Miceuz/triac-bloc/triac bloc top.jpg

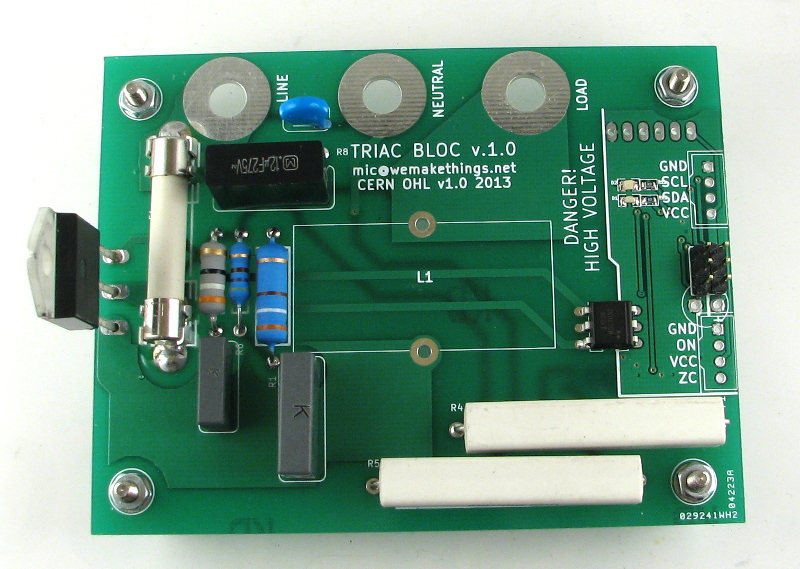
triac bloc top.jpg
