Miceuz/triac-bloc/zc-scope.png

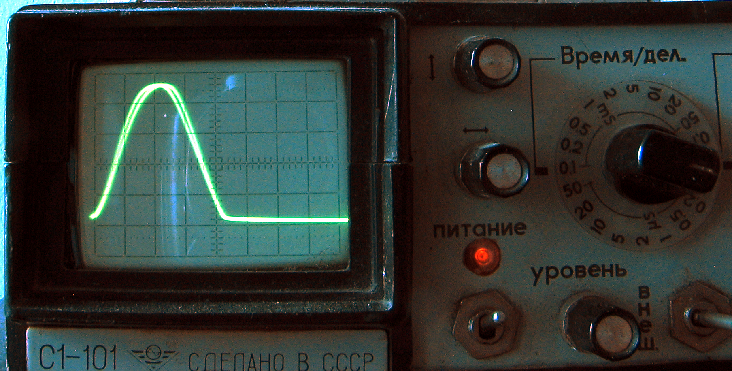
zc-scope.png
