Miceuz/triac-bloc/power-vs-cond-angle.png

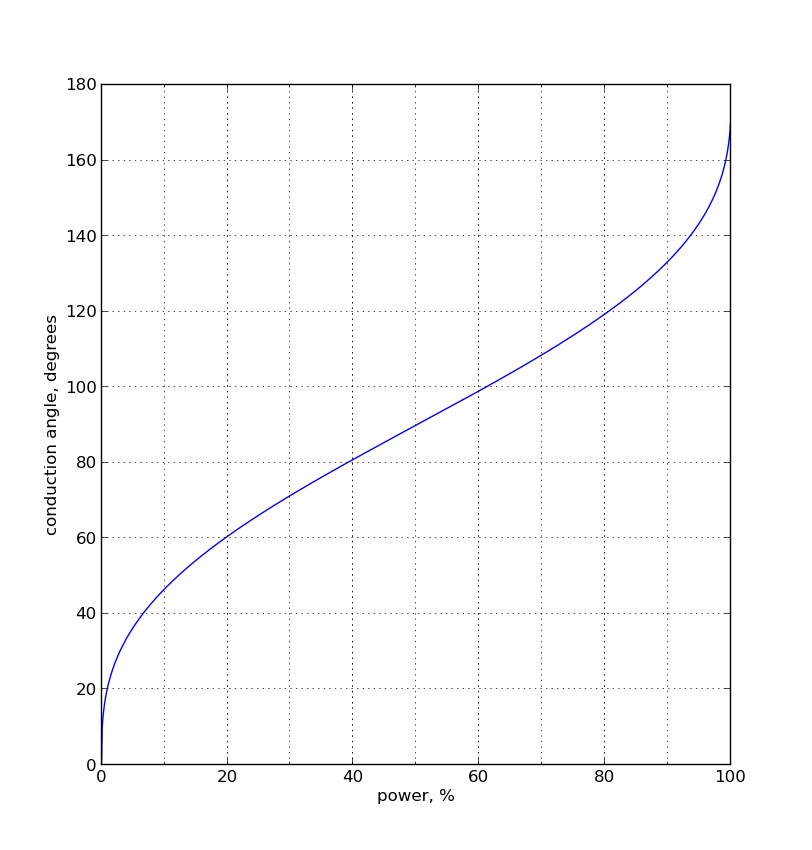
power-vs-cond-angle.png
