Miceuz/triac-bloc/ssr.png

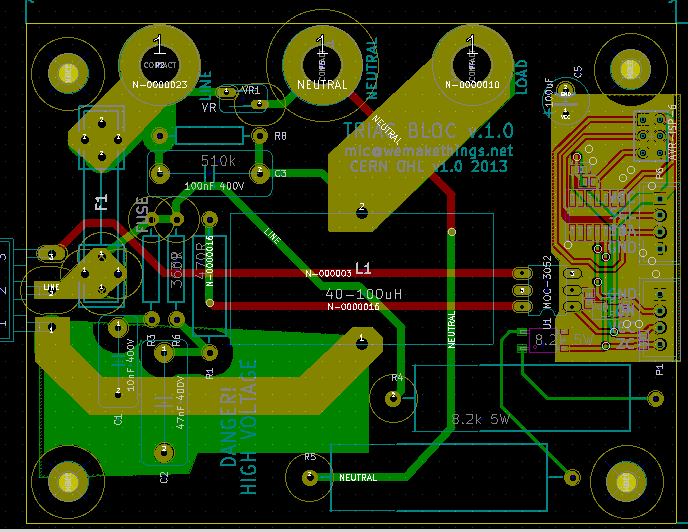
ssr.png
