Miceuz/triac-bloc/triac bloc bottom.jpg

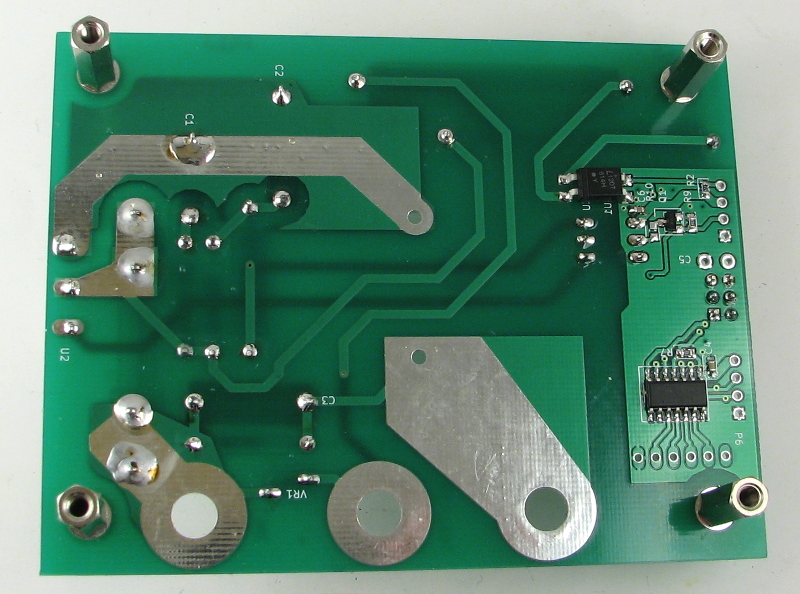
triac bloc bottom.jpg
