Miceuz/triac-bloc/experiment1/impulse-response-linear.png

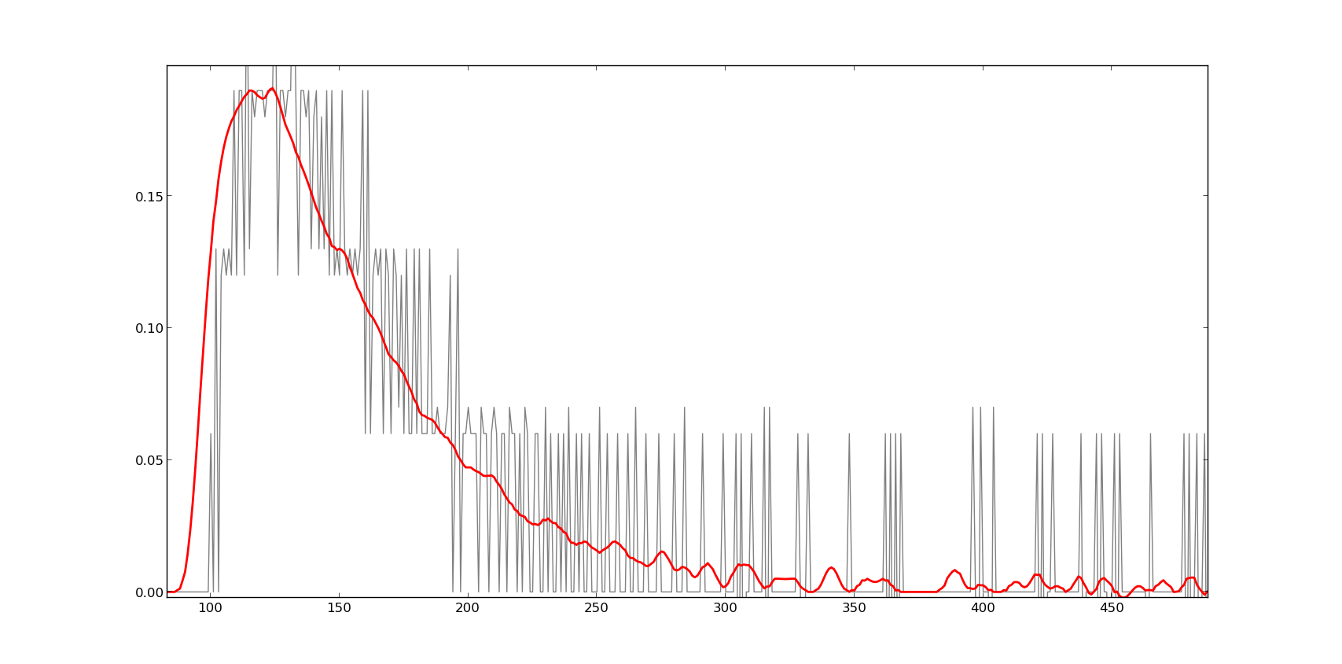
experiment1/impulse-response-linear.png
