Miceuz/triac-bloc/experiment2/period-length-filtered.png

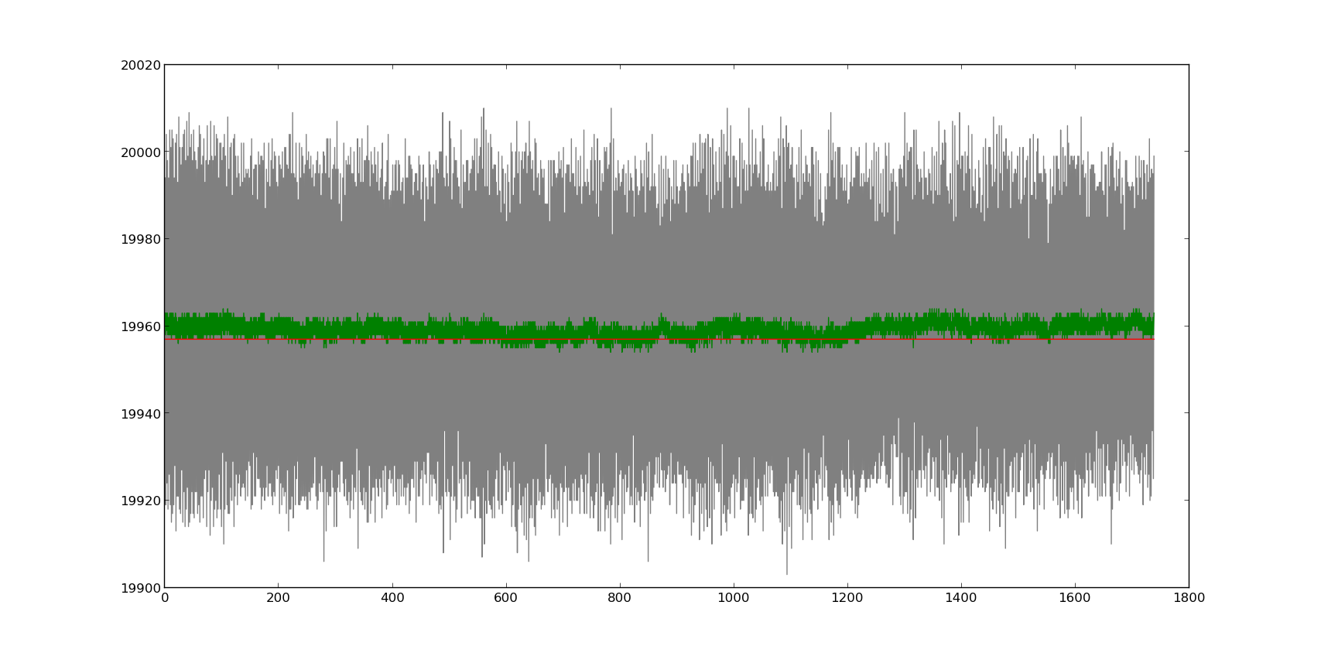
experiment2/period-length-filtered.png
