Miceuz/triac-bloc/experiment2/zc-pulse-length-noise2.png

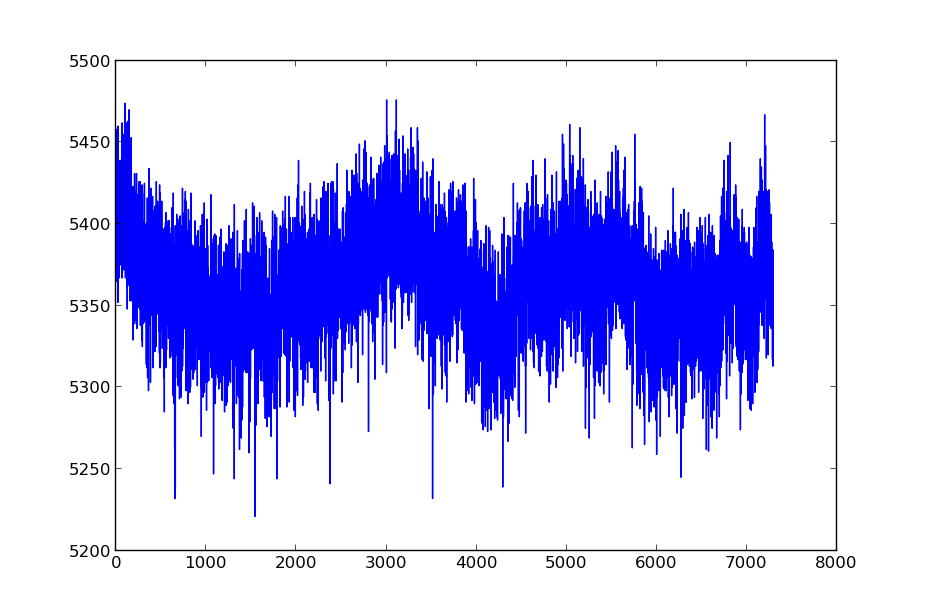
experiment2/zc-pulse-length-noise2.png
