Miceuz/triac-bloc/experiment2/Zero crossing pulse length, R input = 16k4 R pullup = 1k.png

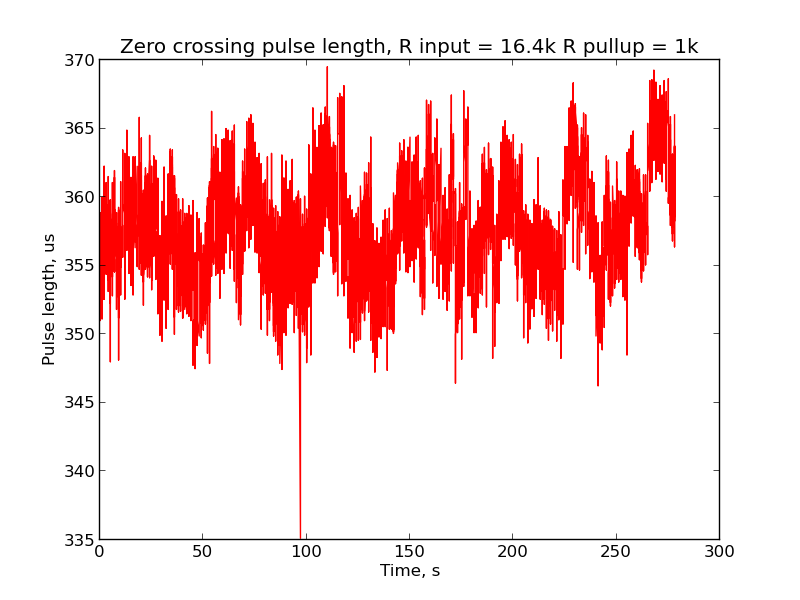
experiment2/Zero crossing pulse length, R input = 16k4 R pullup = 1k.png
