Miceuz/triac-bloc/experiment2/Zero crossing pulse length, R input = 32k8, R pullup = 47k.png

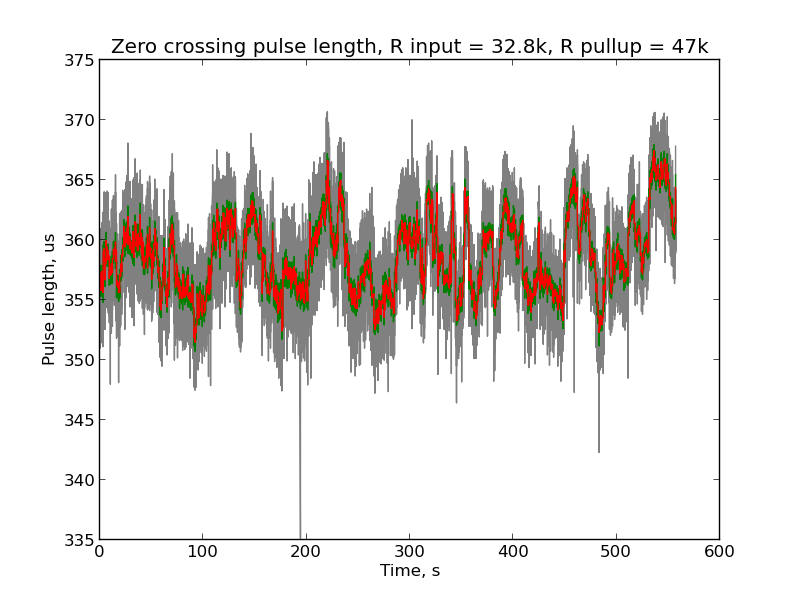
experiment2/Zero crossing pulse length, R input = 32k8, R pullup = 47k.png
