Miceuz/triac-bloc/experiment3/Pulse length differeces for adjacent pulses, R input = 32k8 R pullup = 10k.png

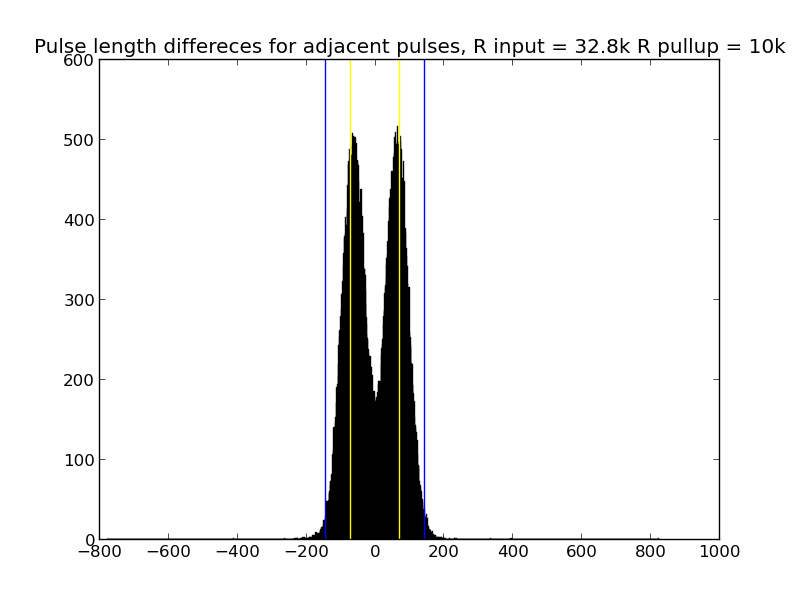
experiment3/Pulse length differeces for adjacent pulses, R input = 32k8 R pullup = 10k.png
