Miceuz/triac-bloc/experiment3/Zero crossing pulse length, R input = 16k4 R pullup = 1k.png

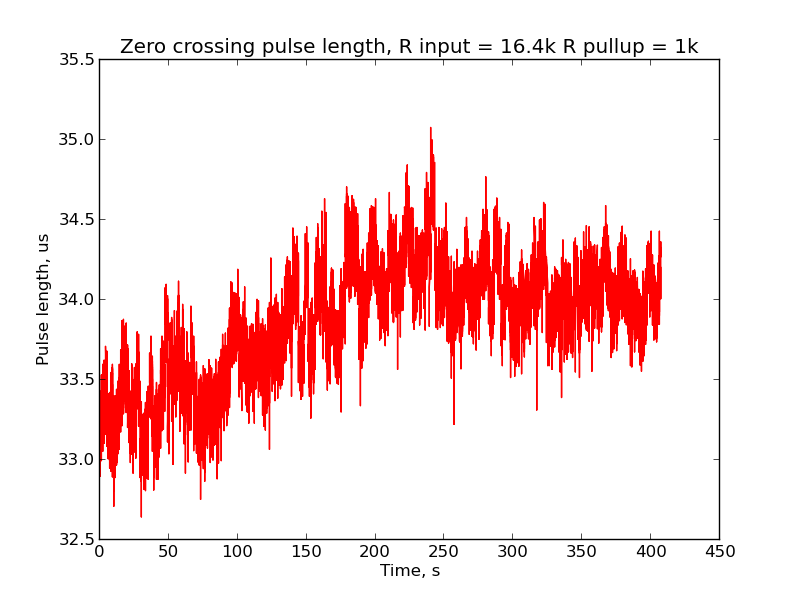
experiment3/Zero crossing pulse length, R input = 16k4 R pullup = 1k.png
