Miceuz/triac-bloc/experiment3/Zero crossing pulse length, R input = 32k8, R pullup = 10k.png

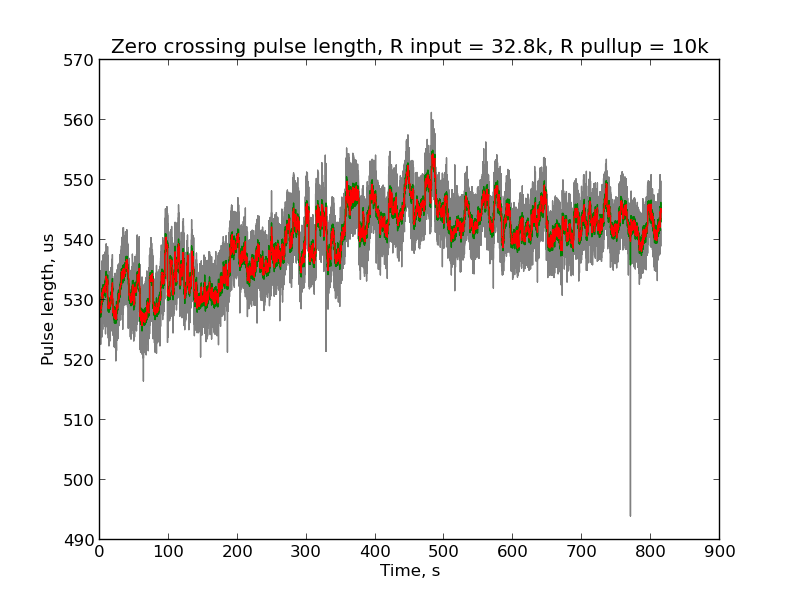
experiment3/Zero crossing pulse length, R input = 32k8, R pullup = 10k.png
