Miceuz/triac-bloc/experiment4/Pulse length differeces for adjacent pulses, R input = 16k4 R pullup = 10k.png

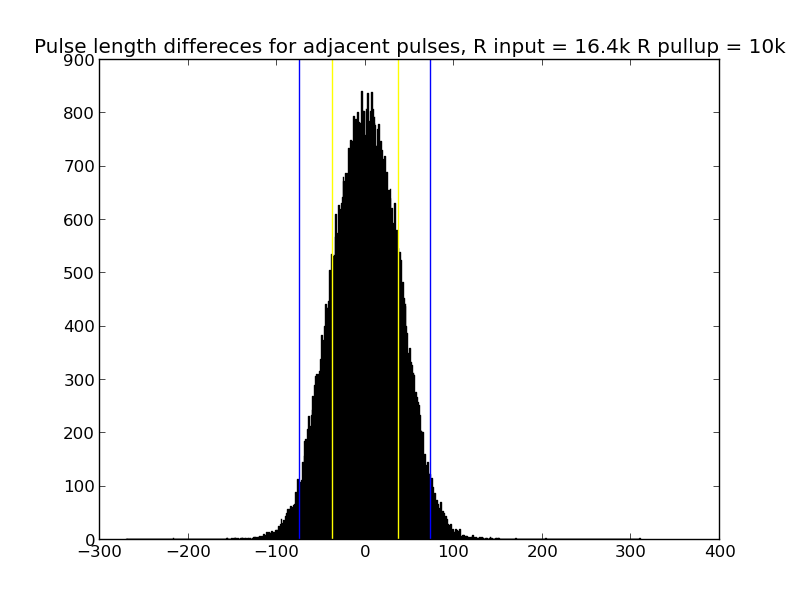
experiment4/Pulse length differeces for adjacent pulses, R input = 16k4 R pullup = 10k.png
