Miceuz/triac-bloc/experiment4/Zero crossing pulse length FFT, R input = 16k4 R pullup = 10k.png

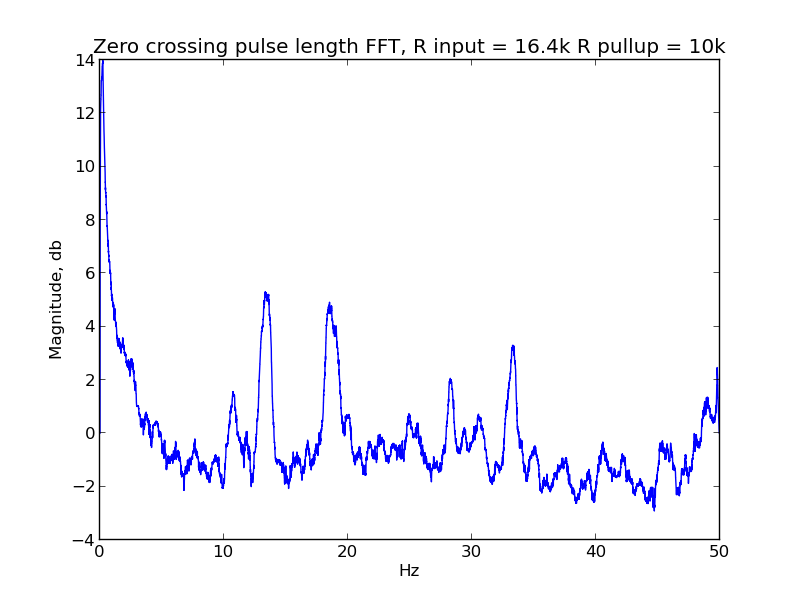
experiment4/Zero crossing pulse length FFT, R input = 16k4 R pullup = 10k.png
