Miceuz/triac-bloc/experiment5/Pulse length differeces for adjacent pulses, R input = 16k4 R pullup = 1k.png

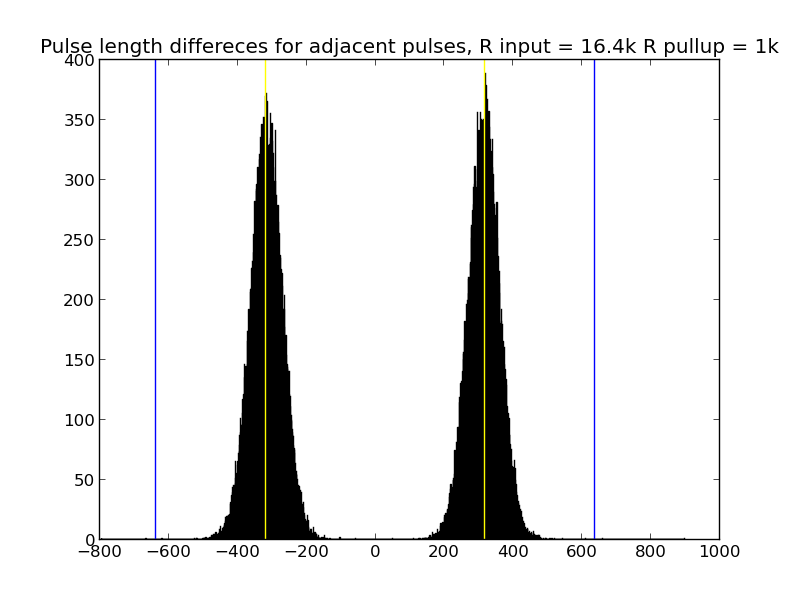
experiment5/Pulse length differeces for adjacent pulses, R input = 16k4 R pullup = 1k.png
