Miceuz/triac-bloc/experiment5/Zero crossing pulse length FFT, R input = 16k4 R pullup = 1k.png

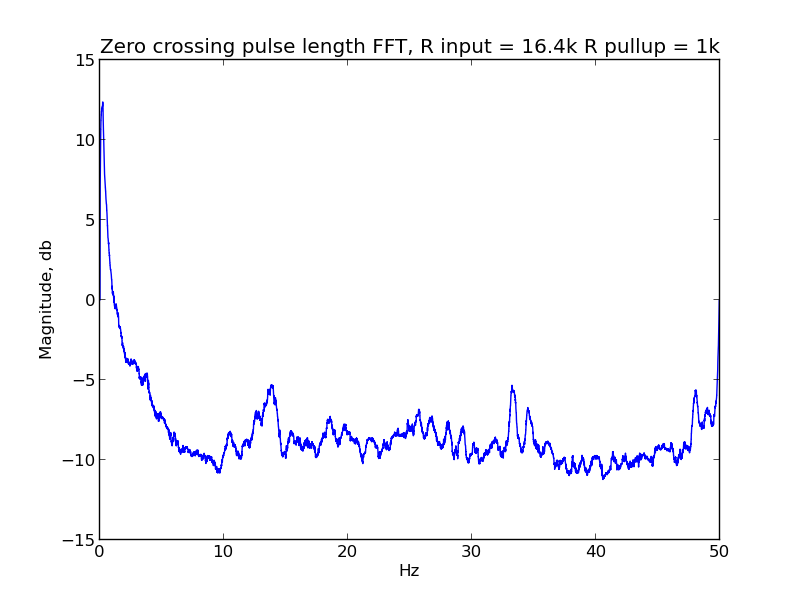
experiment5/Zero crossing pulse length FFT, R input = 16k4 R pullup = 1k.png
