Miceuz/triac-bloc/experiment6/Pulse length differeces for adjacent pulses, R input = 16k4 R pullup = 10k.png

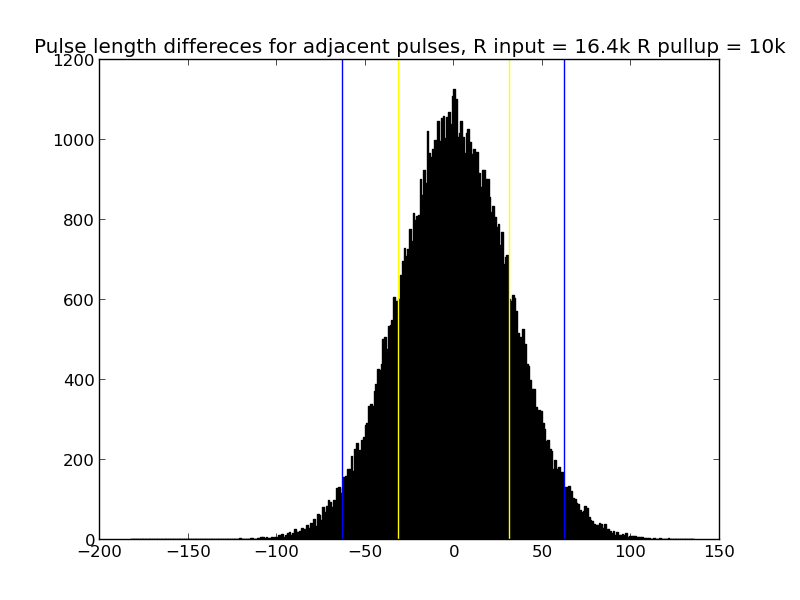
experiment6/Pulse length differeces for adjacent pulses, R input = 16k4 R pullup = 10k.png
