Miceuz/triac-bloc/experiment6/Zero crossing pulse length FFT, R input = 16k4 R pullup = 10k.png

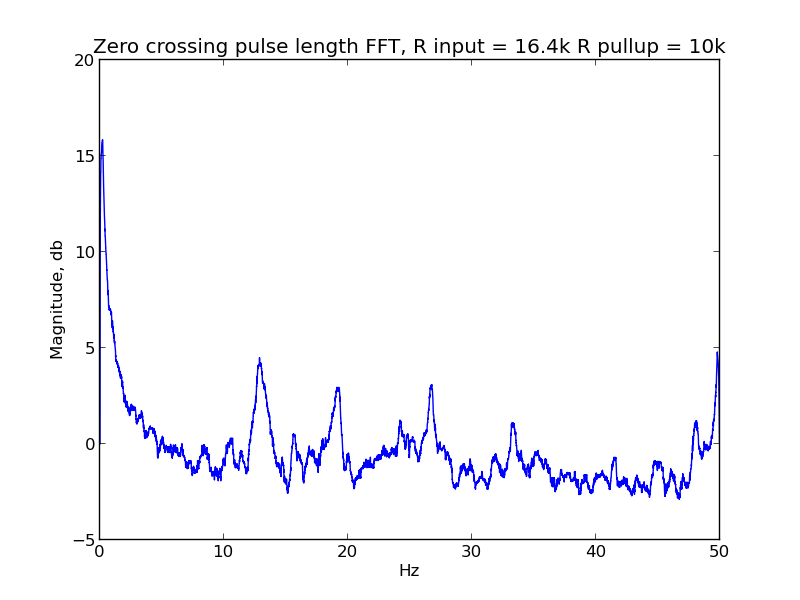
experiment6/Zero crossing pulse length FFT, R input = 16k4 R pullup = 10k.png
