Miceuz/triac-bloc/experiment6/Zero crossing pulse length, R input = 16k4 R pullup = 1k.png

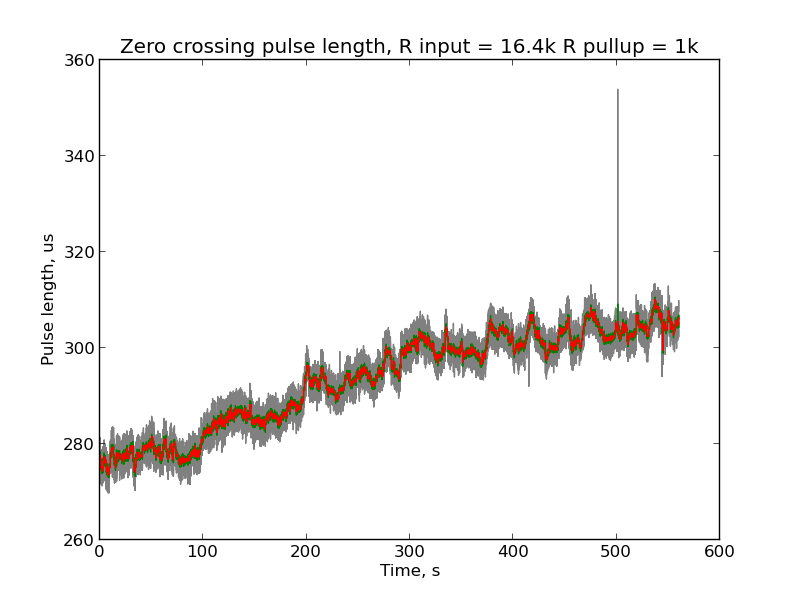
experiment6/Zero crossing pulse length, R input = 16k4 R pullup = 1k.png
