Miceuz/triac-bloc/firmware/conductionAngles.c

#include <inttypes.h>
#include <avr/pgmspace.h>

const uint16_t conductionAngles[] PROGMEM = {
		0 ,
		843 ,
		1066 ,
		1223 ,
		1349 ,
		1459 ,
		1553 ,
		1637 ,
		1714 ,
		1786 ,
		1854 ,
		1916 ,
		1976 ,
		2032 ,
		2087 ,
		2138 ,
		2188 ,
		2235 ,
		2281 ,
		2327 ,
		2370 ,
		2412 ,
		2452 ,
		2492 ,
		2532 ,
		2570 ,
		2606 ,
		2643 ,
		2679 ,
		2714 ,
		2748 ,
		2781 ,
		2814 ,
		2847 ,
		2879 ,
		2910 ,
		2941 ,
		2972 ,
		3002 ,
		3032 ,
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
};
